clovisf/ESP32-C6-development-board/Images/breadboard.jpg

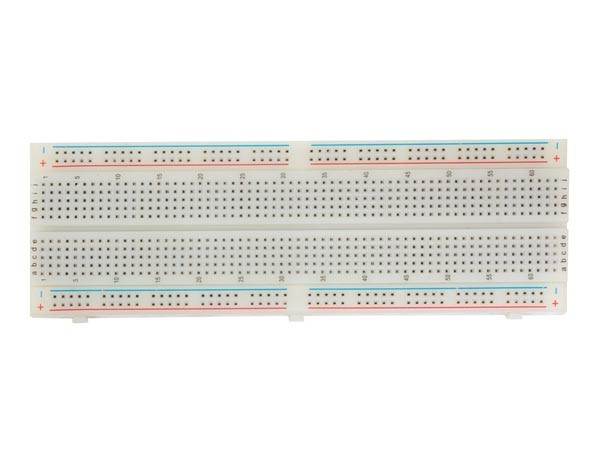
Images/breadboard.jpg
