clovisf/ESP32-C6-development-board/Images/diagrama-esquematico-dev-board-esp32-c6.png

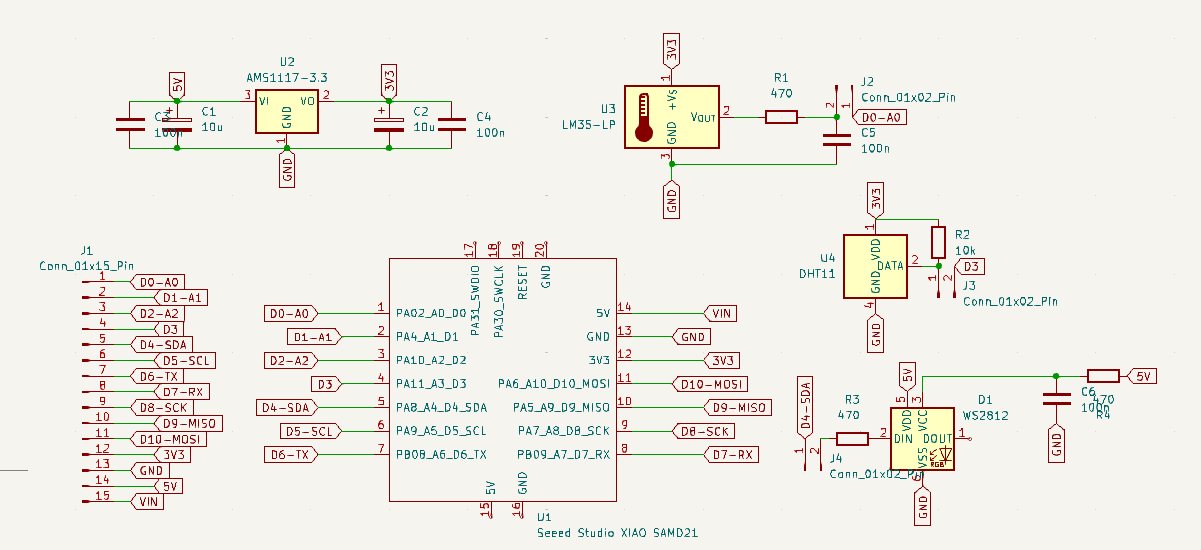
Images/diagrama-esquematico-dev-board-esp32-c6.png
