clovisf/ESP32-C6-development-board/Schematic and PCB/ESP32C6-dev-board.kicad_sch

## KiCad design Schematic and PCB/ESP32C6-dev-board.kicad_sch (2024-10-16)

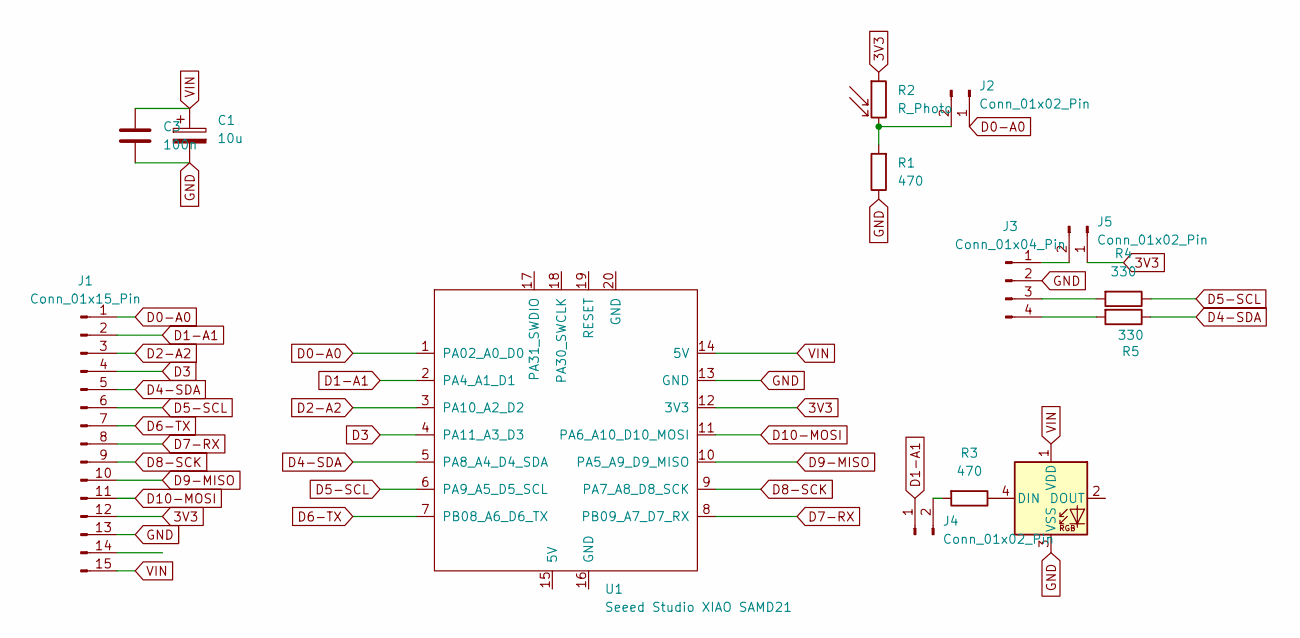
[picture p9: schematic ESP32C6-dev-board.kicad_sch]

Parts:
C1: 10u; CP_Elec_4x5.4
C3: 100n; C_0805_2012Metric
D2: WS2812B; LED_WS2812B_PLCC4_5.0x5.0mm_P3.2mm
J1: Conn_01x15_Pin; PinHeader_1x15_P2.54mm_Vertical
J2, J4, J5: Conn_01x02_Pin; PinHeader_1x02_P2.54mm_Vertical
J3: Conn_01x04_Pin; PinHeader_1x04_P2.54mm_Vertical
R1, R3: 470; R_0805_2012Metric
R2: R_Photo; R_LDR_5.0x4.1mm_P3mm_Vertical
R4, R5: 330; R_0805_2012Metric
U1: Seeed Studio XIAO SAMD21; Seeeduino XIAO-MOUDLE14P-2.54-21X17.8MM

Connections:
3V3: J1.12, J5.1, R2.1, U1.12 (3V3)
D0-A0: J1.1, J2.1, U1.1 (PA02_A0_D0)
D1-A1: J1.2, J4.1, U1.2 (PA4_A1_D1)
D2-A2: J1.3, U1.3 (PA10_A2_D2)
D3: J1.4, U1.4 (PA11_A3_D3)
D4-SDA: J1.5, R5.1, U1.5 (PA8_A4_D4_SDA)
D5-SCL: J1.6, R4.1, U1.6 (PA9_A5_D5_SCL)
D6-TX: J1.7, U1.7 (PB08_A6_D6_TX)
D7-RX: J1.8, U1.8 (PB09_A7_D7_RX)
D8-SCK: J1.9, U1.9 (PA7_A8_D8_SCK)
D9-MISO: J1.10, U1.10 (PA5_A9_D9_MISO)
D10-MOSI: J1.11, U1.11 (PA6_A10_D10_MOSI)
GND: C1.2, C3.2, D2.3 (VSS), J1.13, J3.2, R1.1, U1.13 (GND)
unnamed: D2.4 (DIN), R3.1
unnamed: J2.2, R1.2, R2.2
unnamed: J3.1, J5.2
unnamed: J3.3, R4.2
unnamed: J3.4, R5.2
unnamed: J4.2, R3.2
VIN: C1.1, C3.1, D2.1 (VDD), J1.15, U1.14 (5V)
